zedoCN/Keyboard-Nilou/img/IMG_20230527_031405.jpg

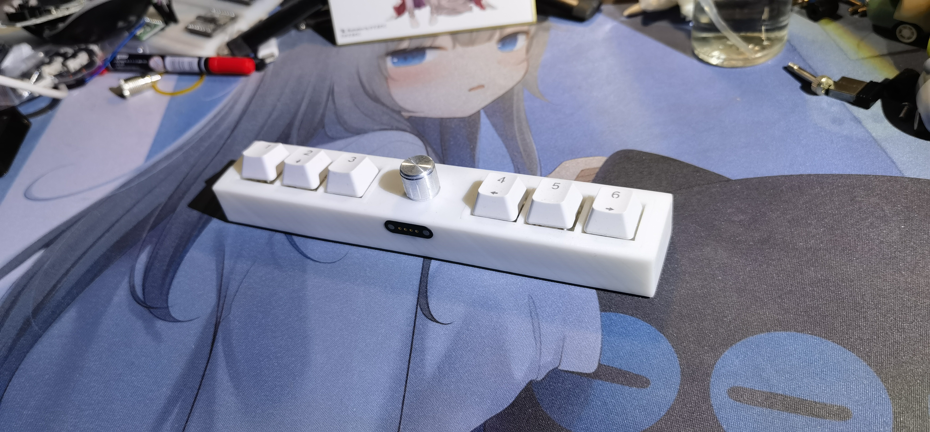
img/IMG_20230527_031405.jpg
