zedoCN/Keyboard-Nilou/img/IMG_20230527_032231.jpg

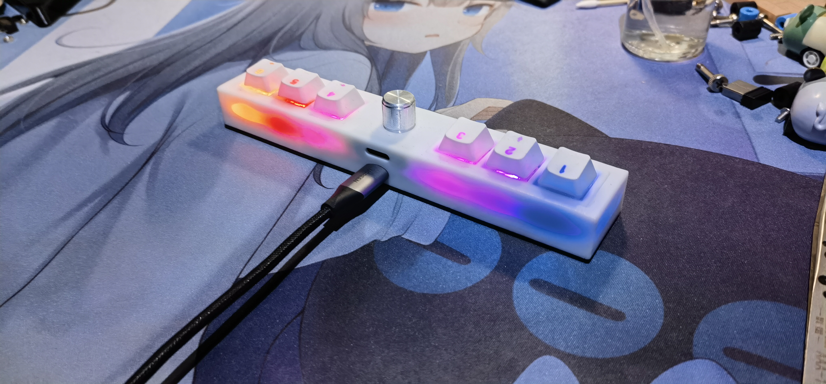
img/IMG_20230527_032231.jpg
