zedoCN/Keyboard-Nilou/PCB_PCB_键盘外设_1.0V_2022-09-01-2.png

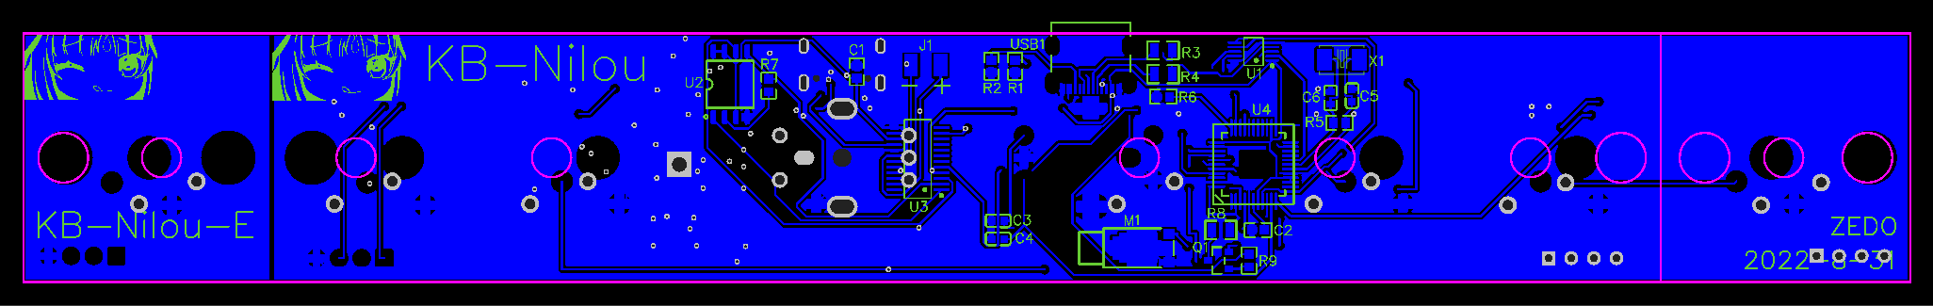
PCB_PCB_键盘外设_1.0V_2022-09-01-2.png
